TylerSeiford/CorsairController/SimpleFanController.cpp

#include "SimpleFanController.h"
#include <EEPROM.h>

SimpleFanController::SimpleFanController(TemperatureController* temperatureController, uint16_t updateRate, uint16_t eEPROMAdress) : temperatureController(temperatureController), updateRate(updateRate), eEPROMAdress(eEPROMAdress)
{
	load();
}

void SimpleFanController::addFan(uint8_t index, IFan* fan)
{
	if (index >= FAN_NUM) {
		return;
	}
	fans[index] = fan;
	switch (fanData[index].mode)
	{
	case FAN_CONTROL_MODE_FIXED_POWER:
		fanData[index].speed = fan->calculateSpeedFromPower(fanData[index].power);
		break;
	case FAN_CONTROL_MODE_FIXED_RPM:
		fanData[index].power = fan->calculatePowerFromSpeed(fanData[index].speed);
		break;
	}

	fanData[index].detectionType = fan->getType();
}

bool SimpleFanController::updateFans()
{
	long currentUpdate = millis();
	long lastUpdateNumber = lastUpdate / updateRate;
	long currentUpdateNumber = currentUpdate / updateRate;
	lastUpdate = currentUpdate;
	if (lastUpdateNumber < currentUpdateNumber) {
		if (trigger_save) {
			trigger_save = false;
			save();
		}

		for (uint8_t i = 0; i < FAN_NUM; i++) {
			if (fans[i] == NULL) {
				continue;
			}
			if (fanData[i].mode == FAN_CONTROL_MODE_FIXED_RPM || fanData[i].mode == FAN_CONTROL_MODE_FIXED_POWER) {
				fans[i]->setPower(fanData[i].power);
				continue;
			}

			uint16_t temp;
			const uint8_t& group = fanData[i].tempGroup;
			if (group == FAN_CURVE_TEMP_GROUP_EXTERNAL) {
				temp = externalTemp[i];
			}
			else if (group < TEMPERATURE_NUM) {
				temp = temperatureController->getTemperature(group);
			}

			const FanCurve& fanCurve = fanData[i].fanCurve;
			uint16_t speed;

			if (temp <= fanCurve.temperatures[0]) {
				speed = fanCurve.rpms[0];
			}
			else if (temp > fanCurve.temperatures[FAN_CURVE_POINTS_NUM - 1]) {
				speed = fanCurve.rpms[FAN_CURVE_POINTS_NUM - 1];
			}
			else {
				for (uint8_t p = 0; p < FAN_CURVE_POINTS_NUM - 1; p++) {
					if (temp > fanCurve.temperatures[p + 1]) {
						continue;
					}
					speed = map(temp, fanCurve.temperatures[p], fanCurve.temperatures[p + 1], fanCurve.rpms[p], fanCurve.rpms[p + 1]);
					break;
				}
			}

			fanData[i].speed = speed;
			fanData[i].power = fans[i]->calculatePowerFromSpeed(speed);
			fans[i]->setPower(fanData[i].power);
		}
		return true;
	}
	return false;
}

uint16_t SimpleFanController::getFanSpeed(uint8_t fan)
{
	return fanData[fan].speed;
}

void SimpleFanController::setFanSpeed(uint8_t fan, uint16_t speed)
{
	fanData[fan].speed = speed;
	fanData[fan].mode = FAN_CONTROL_MODE_FIXED_RPM;
	fanData[fan].power = fans[fan] != NULL ? fans[fan]->calculatePowerFromSpeed(speed) : 0;
	trigger_save = true;
}

uint8_t SimpleFanController::getFanPower(uint8_t fan)
{
	return fanData[fan].power;
}

void SimpleFanController::setFanPower(uint8_t fan, uint8_t percentage)
{
	fanData[fan].power = percentage;
	fanData[fan].mode = FAN_CONTROL_MODE_FIXED_POWER;
	fanData[fan].speed = fans[fan] != NULL ? fans[fan]->calculateSpeedFromPower(percentage) : 0;
	trigger_save = true;
}

void SimpleFanController::setFanCurve(uint8_t fan, uint8_t group, FanCurve& fanCurve)
{
	fanData[fan].fanCurve = fanCurve;
	fanData[fan].tempGroup = group;
	fanData[fan].mode = FAN_CONTROL_MODE_CURVE;
	trigger_save = true;
}

void SimpleFanController::setFanExternalTemperature(uint8_t fan, uint16_t temp)
{
	externalTemp[fan] = temp;
}

void SimpleFanController::setFanForce3PinMode(bool flag)
{
	force3PinMode = flag;
}

uint8_t SimpleFanController::getFanDetectionType(uint8_t fan)
{
	return fanData[fan].detectionType;
}

void SimpleFanController::setFanDetectionType(uint8_t fan, uint8_t type)
{
	if (fanData[fan].detectionType != type) {
		fanData[fan].detectionType = type;
		trigger_save = true;
	}
}

bool SimpleFanController::load()
{
	EEPROM.get(eEPROMAdress, fanData);
	return true;
}

bool SimpleFanController::save()
{
#ifdef DEBUG
	Serial.println(F("Save fan data to EEPROM."));
#endif
	EEPROM.put(eEPROMAdress, fanData);
	return true;
}
